Yowkees/keyball/keyball39/doc/rev1/images/kb39_111.jpg

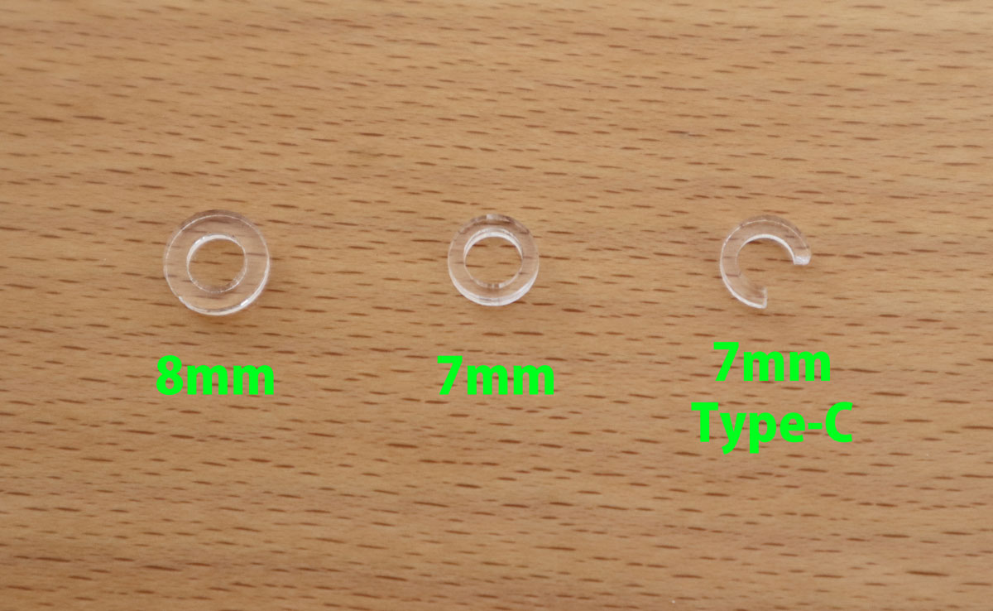
keyball39/doc/rev1/images/kb39_111.jpg
