Yowkees/keyball/keyball39/doc/rev1/images/kb39_140.jpg

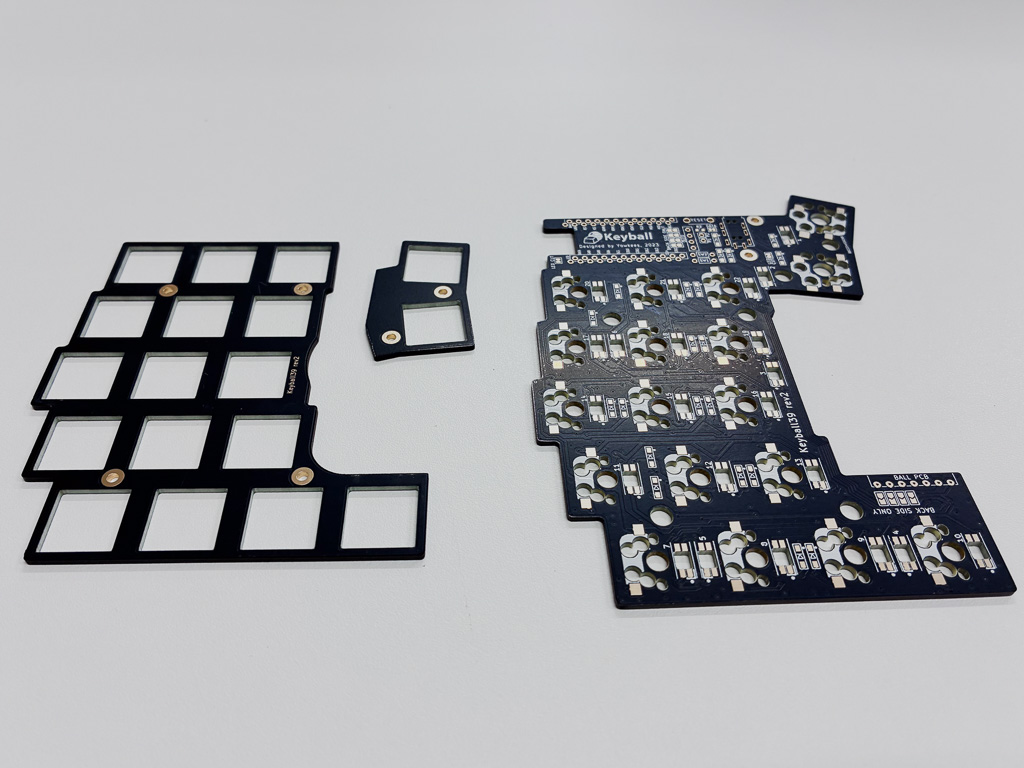
keyball39/doc/rev1/images/kb39_140.jpg
