Yowkees/keyball/keyball44/doc/rev1/images/kb39_137.jpg

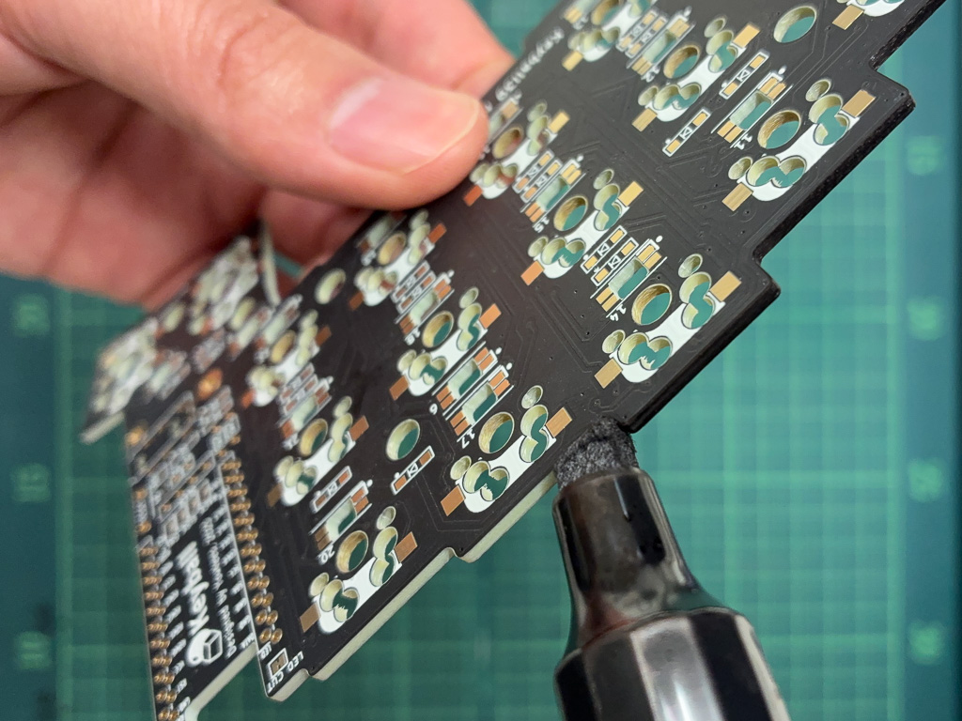
keyball44/doc/rev1/images/kb39_137.jpg
