Yowkees/keyball/keyball44/doc/rev1/images/kb44_036.jpg

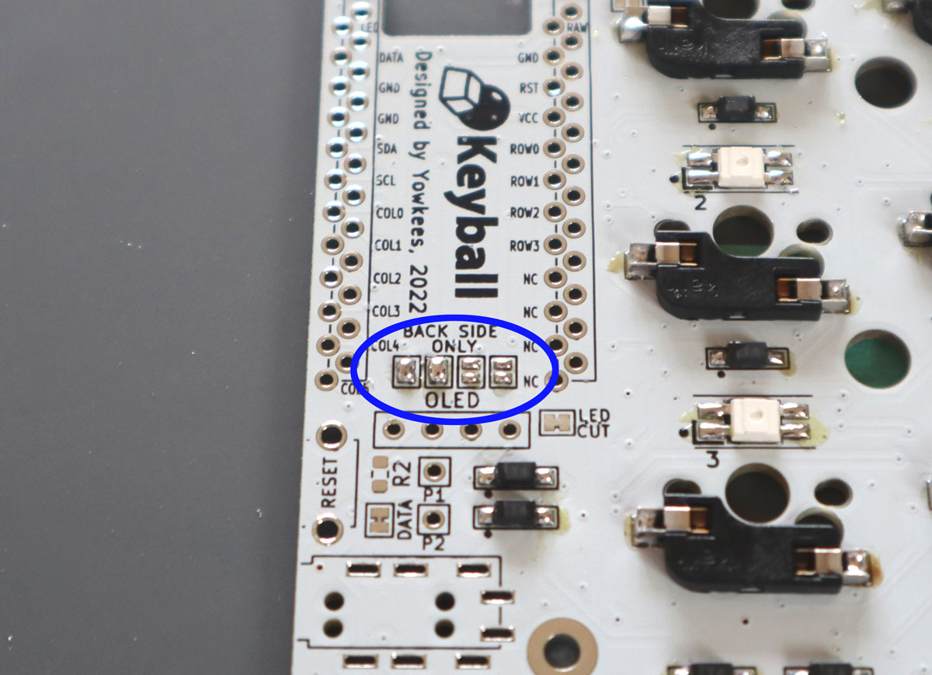
keyball44/doc/rev1/images/kb44_036.jpg
