Yowkees/keyball/keyball44/doc/rev1/images/kb44_069.jpg

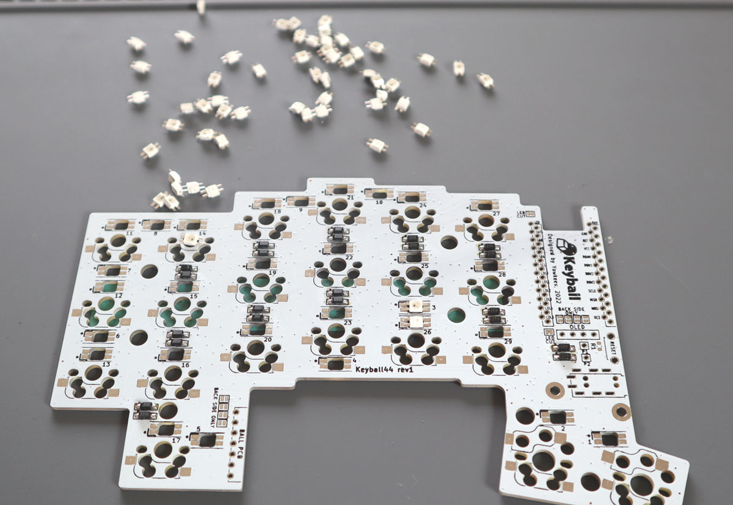
keyball44/doc/rev1/images/kb44_069.jpg
