Yowkees/keyball/keyball44/doc/rev1/images/kb44_072.jpg

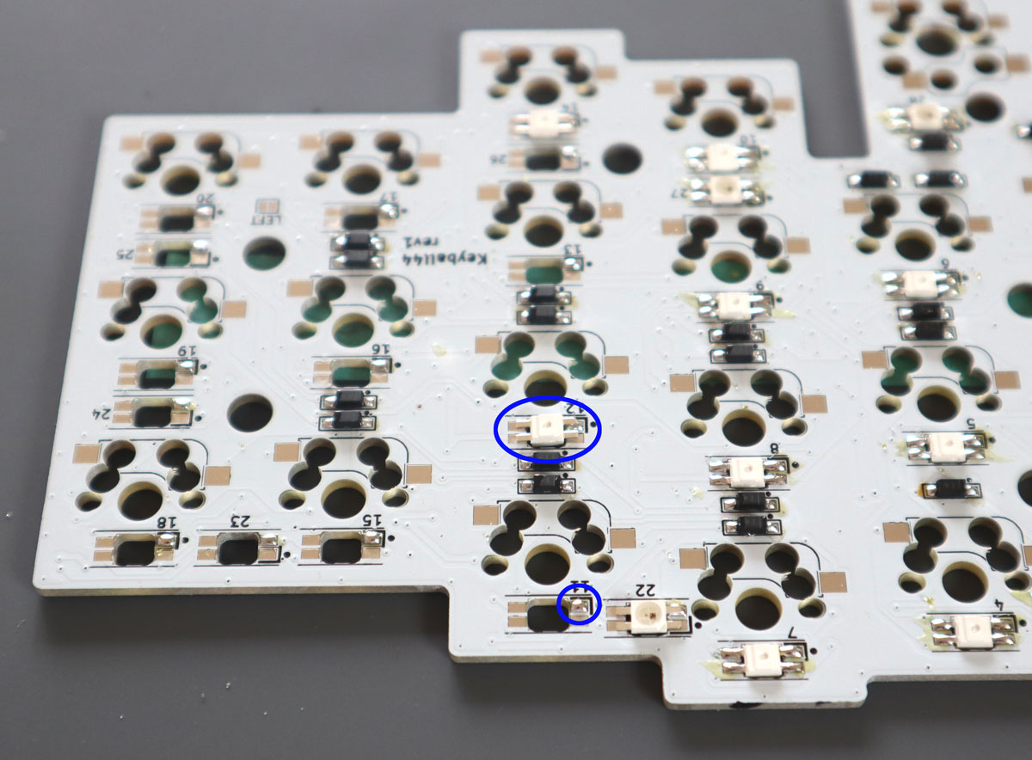
keyball44/doc/rev1/images/kb44_072.jpg
