Yowkees/keyball/keyball46/doc/rev1/images/yw029.jpg

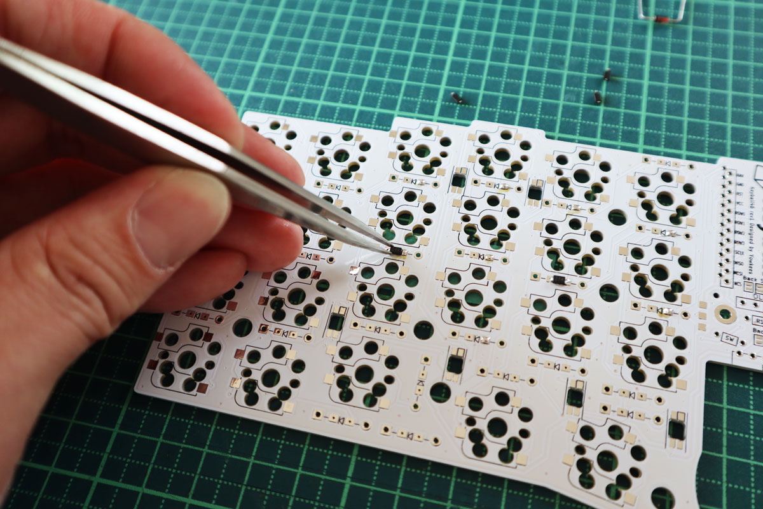
keyball46/doc/rev1/images/yw029.jpg
