Yowkees/keyball/keyball61/doc/rev1/images/kb61_006.jpg

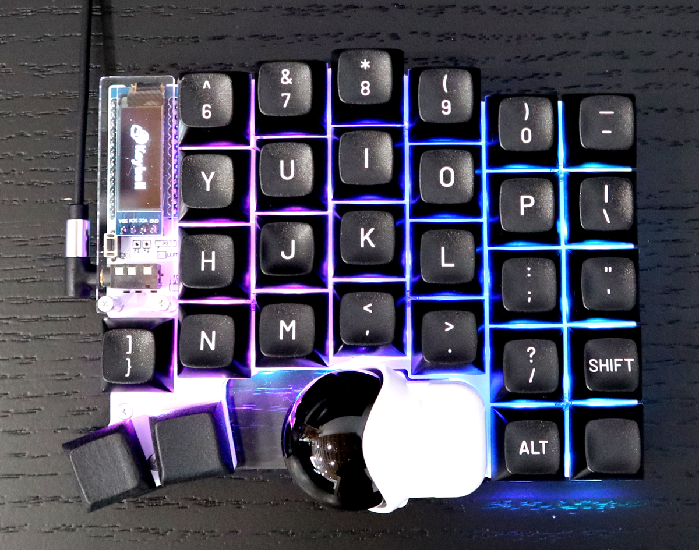
keyball61/doc/rev1/images/kb61_006.jpg
