Yowkees/keyball/Keybit8/doc/rev1/images/_MG_8246.jpg

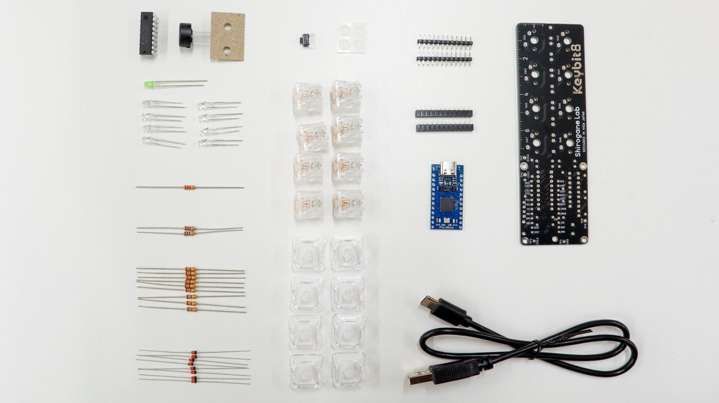
Keybit8/doc/rev1/images/_MG_8246.jpg
