Yowkees/keyball/Keybit8/doc/rev1/images/_MG_8316.jpg

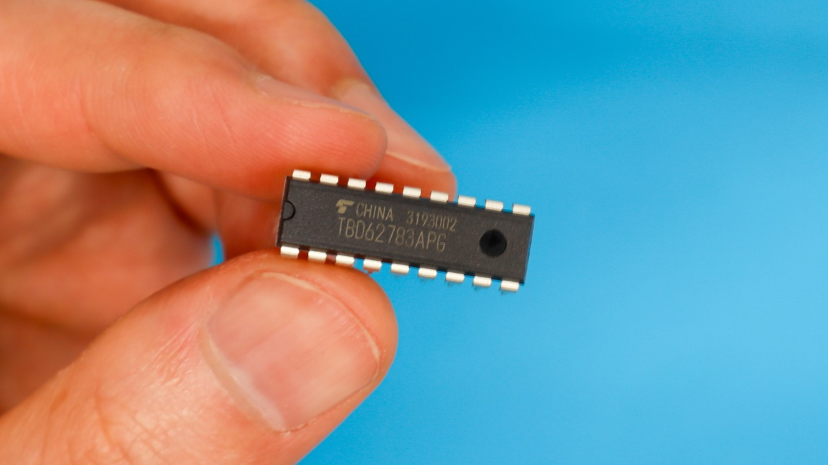
Keybit8/doc/rev1/images/_MG_8316.jpg
