Yowkees/keyball/Keybit8/doc/rev1/images/_MG_8327-3.jpg

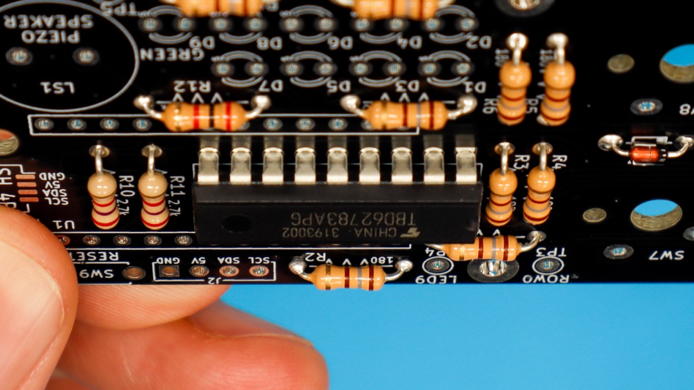
Keybit8/doc/rev1/images/_MG_8327-3.jpg
