Yowkees/keyball/Keybit8/doc/rev1/images/_MG_8330.jpg

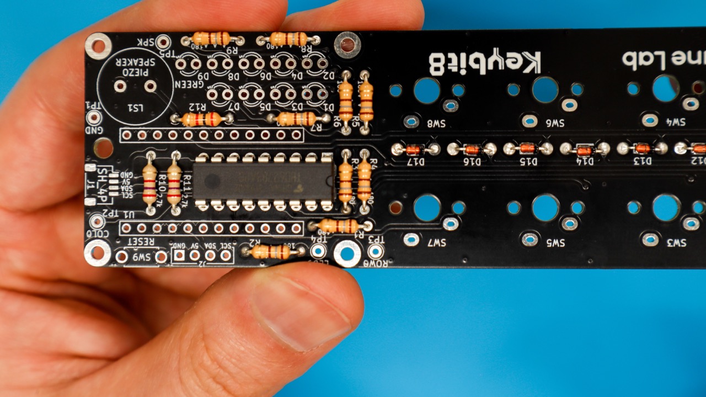
Keybit8/doc/rev1/images/_MG_8330.jpg
