Yowkees/keyball/Keybit8/doc/rev1/images/_MG_8380-2.jpg

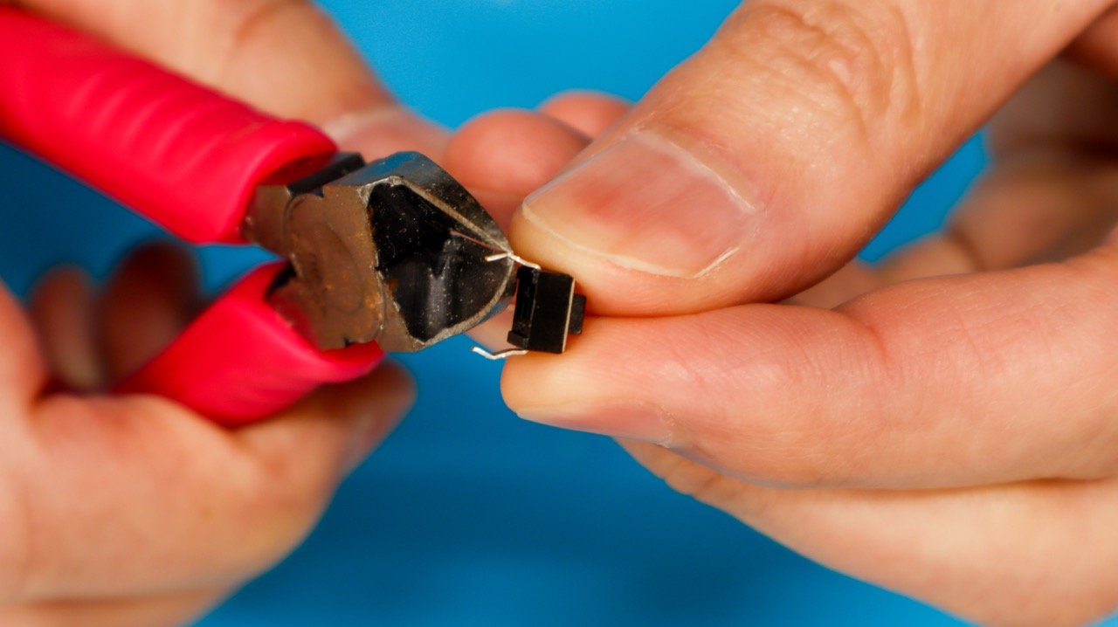
Keybit8/doc/rev1/images/_MG_8380-2.jpg
