Yowkees/keyball/qmk_firmware/keyboards/keyball/one47/docs/apply-kemap-right-to-left.png

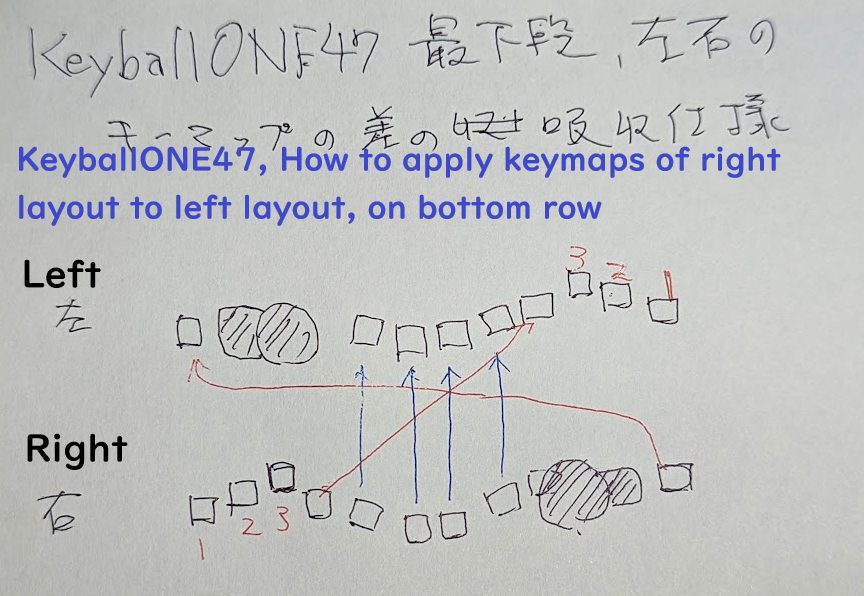
qmk_firmware/keyboards/keyball/one47/docs/apply-kemap-right-to-left.png
